gcgoodwin/CPU/LTSpice/8-Bit-Register.asc

A1: and; td=10n
A2: and; td=10n
A3: and
A4: and; td=10n
A5: and; td=10n
A6.: and; td=10n
A6: and; td=10n
A7: and; td=10n
A8: and; td=10n
A9: and; td=10n
A10: and; td=10n
A11: inv
A12: and; td=10n
A13: and
A14: and; td=10n
A15: and; td=10n
A16: and; td=10n
A17: and; td=10n
A18: and; td=10n
A19: and; td=10n
A20: and; td=10n
A21: inv
A22: and; td=10n
A23: and; td=10n
A24: and
A25: and; td=10n
A26: and; td=10n
A27: and; td=10n
A28: and; td=10n
A29: and; td=10n
A30: and; td=10n
A31: and; td=10n
A32: inv
A33: and; td=10n
A34: and; td=10n
A35: and
A36: and; td=10n
A37: and; td=10n
A38: and; td=10n
A39: and; td=10n
A40: and; td=10n
A41: and; td=10n
A42: and; td=10n
A43: inv
A44: and; td=10n
A45: and; td=10n
A46: and
A47: and; td=10n
A48: and; td=10n
A49: and; td=10n
A50: and; td=10n
A51: and; td=10n
A52: and; td=10n
A53: and; td=10n
A54: inv
A55: and; td=10n
A56: and; td=10n
A57: and
A58: and; td=10n
A59: and; td=10n
A60: and; td=10n
A61: and; td=10n
A62: and; td=10n
A63: and; td=10n
A64: and; td=10n
A65: inv
A66: and; td=10n
A67: and; td=10n
A68: and
A69: and; td=10n
A70: and; td=10n
A71: and; td=10n
A72: and; td=10n
A73: and; td=10n
A74: and; td=10n
A75: and; td=10n
A76: inv
A77: and; td=10n
A78: and; td=10n
A79: and
A80: and; td=10n
A81: and; td=10n
A82: and; td=10n
A83: and; td=10n
A84: and; td=10n
A85: and; td=10n
A86: and; td=10n
A87: inv
A88: inv
A89: and
A90: and
A91: or
A92: inv
A93: and
A94: and
A95: or
A96: inv
A97: and
A98: and
A99: or
A100: inv
A101: and
A102: and
A103: or
A104: inv
A105: and
A106: and
A107: or
A108: inv
A109: and
A110: and
A111: or
A112: inv
A113: and
A114: and
A115: or
A116: inv
A117: and
A118: and
A119: or
CLOCK2: voltage; PULSE(0 1V 0 1n 1n 10u 20u)
Data-0: voltage; 1
Data-1: voltage; 0
Data-2: voltage; 1
Data-3: voltage; 0
Data-4: voltage; 1
Data-5: voltage; 0
Data-6: voltage; 1
Data-7: voltage; 0
LOAD: voltage; PULSE(1 0 50u 1n 1n 50u 100u)
Named nets: MQ0, MQ-0, SQ-0, Q-0, 0, MQ1, MQ-1, SQ-1, Q-1, MQ2, MQ-2, SQ-2, Q-2, MQ3, MQ-3, SQ-3, Q-3, MQ4, MQ-4, SQ-4, Q-4, MQ5, MQ-5, SQ-5, Q-5, MQ6, MQ-6, SQ-6, Q-6, MQ7, MQ-7, SQ-7, Q-7
.tran 200u
.tran 200u
