gcgoodwin/CPU/LTSpice/8-bit-ADD-SUBRACT.asc

11: voltage; 1
12: voltage; 0
13: voltage; 1
14: voltage; 0
15: voltage; 0
16: voltage; 0
17: voltage; 0
18: voltage; 0
21: voltage; 1
22: voltage; 1
23: voltage; 0
24: voltage; 0
25: voltage; 0
26: voltage; 0
27: voltage; 0
28: voltage; 0
A1: xor
A2: xor
A3: and
A4: and
A5: or
A6: xor
A7: xor
A8: and
A9: and
A10: or
A11: xor
A12: xor
A13: and
A14: and
A15: or
A16: xor
A17: xor
A18: and
A19: and
A20: or
A21: xor
A22: xor
A23: and
A24: and
A25: or
A26: xor
A27: xor
A28: and
A29: and
A30: or
A31: xor
A32: xor
A33: and
A34: and
A35: or
A36: xor
A37: xor
A38: and
A39: and
A40: or
A41: xor
A42: xor
A43: xor
A44: xor
A45: xor
A46: xor
A47: xor
A48: xor
V1: voltage; 0
Named nets: 0, Sum3, Carry3, Sum2, Carry2, Sum1, Carry1, Sum0, Carry0, Sum7, CarryOut, Sum6, Carry7, Sum5, Carry5, Sum4, Carry4
.tran 160m
