gcgoodwin/CPU/LTSpice/8AND.asc

A0: voltage
A1: voltage
A2: voltage
A3: voltage
A4: voltage
A5: voltage
A6: voltage
A7: voltage
AND0: and
AND1: and
AND2: and
AND3: and
AND4: and
AND5: and
AND6: and
AND7: and
B0: voltage
B1: voltage
B2: voltage
B3: voltage
B4: voltage
B5: voltage
B6: voltage
B7: voltage
Named nets: 0, RA0, RA1, RA2, RA3, RA4, RA5, RA6, RA7
