gcgoodwin/CPU/LTSpice/8NOT.asc

A0: voltage
A1: voltage
A2: voltage
A3: voltage
A4: voltage
A5: voltage
A6: voltage
A7: voltage
INV0: inv
INV1: inv
INV2: inv
INV3: inv
INV4: inv
INV5: inv
INV6: inv
INV7: inv
Named nets: 0, RA0, RA1, RA2, RA3, RA4, RA5, RA6, RA7
