gcgoodwin/CPU/LTSpice/8OR.asc

A0: voltage
A1: voltage
A2: voltage
A3: voltage
A4: voltage
A5: voltage
A6: voltage
A7: voltage
B0: voltage
B1: voltage
B2: voltage
B3: voltage
B4: voltage
B5: voltage
B6: voltage
B7: voltage
OR0: or
OR1: or
OR2: or
OR3: or
OR4: or
OR5: or
OR6: or
OR7: or
Named nets: 0, RA0, RA1, RA2, RA3, RA4, RA5, RA6, RA7
