gcgoodwin/CPU/LTSpice/8SL.asc

A0: voltage
A1: voltage
A2: voltage
A3: voltage
A4: voltage
A5: voltage
A6: voltage
Ground: voltage
Named nets: 0, RA1, RA2, RA3, RA4, RA5, RA6, RA7
