gcgoodwin/CPU/LTSpice/8SR.asc

A1: voltage
A2: voltage
A3: voltage
A4: voltage
A5: voltage
A6: voltage
A7: voltage
Ground: voltage
Named nets: 0, RA0, RA1, RA2, RA3, RA4, RA5, RA6
