gcgoodwin/CPU/LTSpice/8XOR.asc

A0: voltage
A1: voltage
A2: voltage
A3: voltage
A4: voltage
A5: voltage
A6: voltage
A7: voltage
B0: voltage
B1: voltage
B2: voltage
B3: voltage
B4: voltage
B5: voltage
B6: voltage
B7: voltage
XOR0: xor
XOR1: xor
XOR2: xor
XOR3: xor
XOR4: xor
XOR5: xor
XOR6: xor
XOR7: xor
Named nets: 0, RA0, RA1, RA2, RA3, RA4, RA5, RA6, RA7
