gcgoodwin/CPU/LTSpice/ALU.asc

A1SUM: xor
A2SUM: xor
A3SUM: and
A4SUM: and
A5SUM: or
A6SUM: xor
A7SUM: xor
A8SUM: and
A9SUM: and
A10SUM: or
A11: xor
A12: xor
A13: and
A14: and
A15: or
A16SUM: xor
A17: xor
A18: and
A19: and
A20: or
A21: xor
A22: xor
A23: and
A24: and
A25: or
A26: xor
A27: xor
A28: and
A29: and
A30: or
A31: xor
A32: xor
A33: and
A34: and
A35: or
A36: xor
A37: xor
A38: and
A39: and
A40: or
A41: xor
A42: xor
A43: xor
A44: xor
A45: xor
A46: xor
A47: xor
A48: xor
A49: xor
A50: xor
A51: and
A52: and
A53: or
A54: xor
A55: xor
A56: and
A57: and
A58: or
A59: xor
A60: xor
A61: and
A62: and
A63: or
A64: xor
A65: xor
A66: and
A67: and
A68: or
A69: xor
A70: xor
A71: and
A72: and
A73: or
A74: xor
A75: xor
A76: and
A77: and
A78: or
A79: xor
A80: xor
A81: and
A82: and
A83: or
A84: xor
A85: xor
A86: and
A87: and
A88: or
A89: xor
A90: xor
A91: xor
A92: xor
A93: xor
A94: xor
A95: xor
A96: xor
A97: inv
A98: and
A99: and
A100: or
A101: inv
A102: and
A103: and
A104: or
A105: inv
A106: and
A107: and
A108: or
A109: inv
A110: and
A111: and
A112: or
A113: inv
A114: and
A115: and
A116: or
A117: inv
A118: and
A119: and
A120: or
A121: inv
A122: and
A123: and
A124: or
A125: inv
A126: and
A127: and
A128: or
A129: inv
A130: and
A131: and
A132: or
A133: inv
A134: and
A135: and
A136: or
A137: inv
A138: and
A139: and
A140: or
A141: inv
A142: and
A143: and
A144: or
A145: inv
A146: and
A147: and
A148: or
A149: inv
A150: and
A151: and
A152: or
A153: inv
A154: and
A155: and
A156: or
A157: inv
A158: and
A159: and
A160: or
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
.tran 0 80m 0 10u
